MartinDrillon/ITEMX/docs/images/key2.jpg

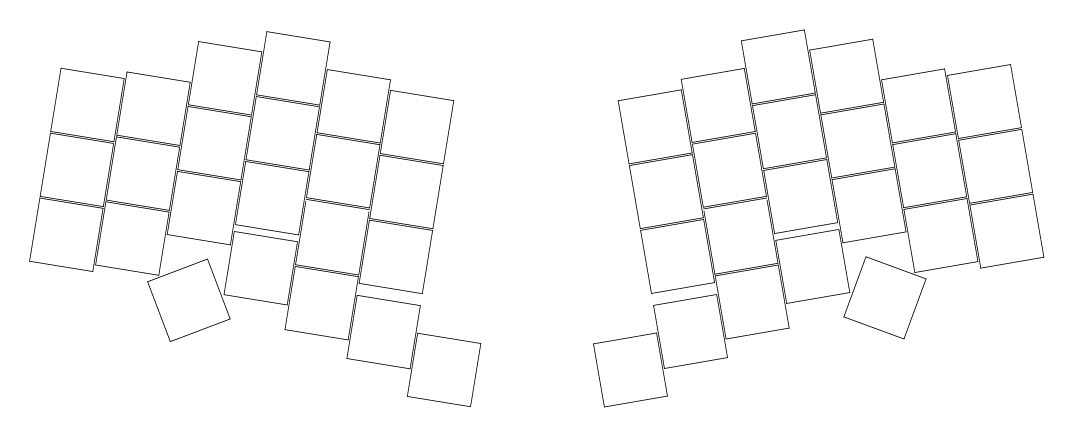
docs/images/key2.jpg
